Pravuz/AimBot/3D model/Rendered images/Back view.JPG

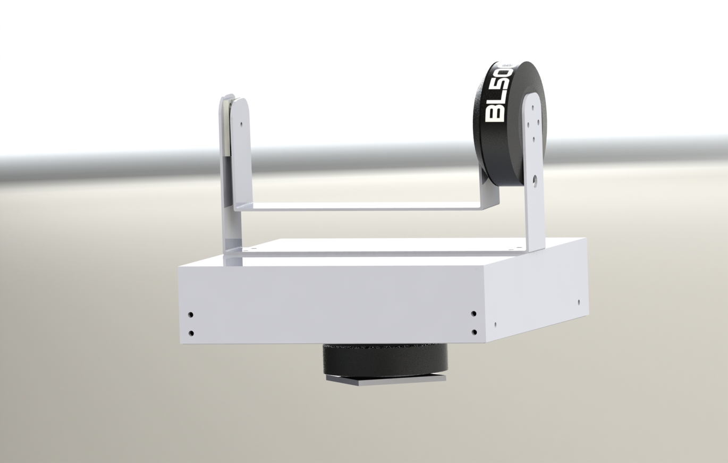
3D model/Rendered images/Back view.JPG
