Pravuz/AimBot/3D model/Rendered images/Bearing and bracket.JPG

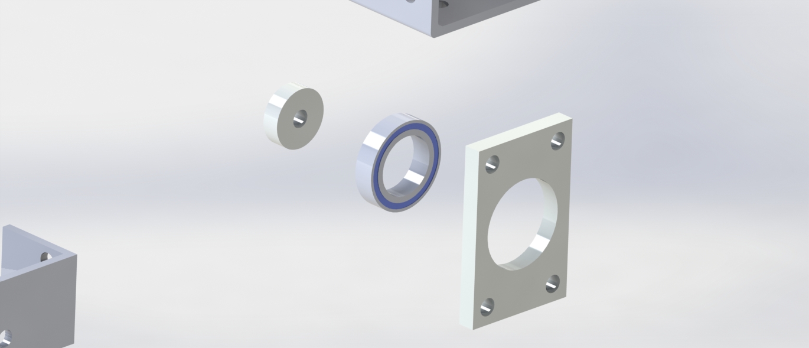
3D model/Rendered images/Bearing and bracket.JPG
