Pravuz/AimBot/3D model/Rendered images/Bottom.JPG

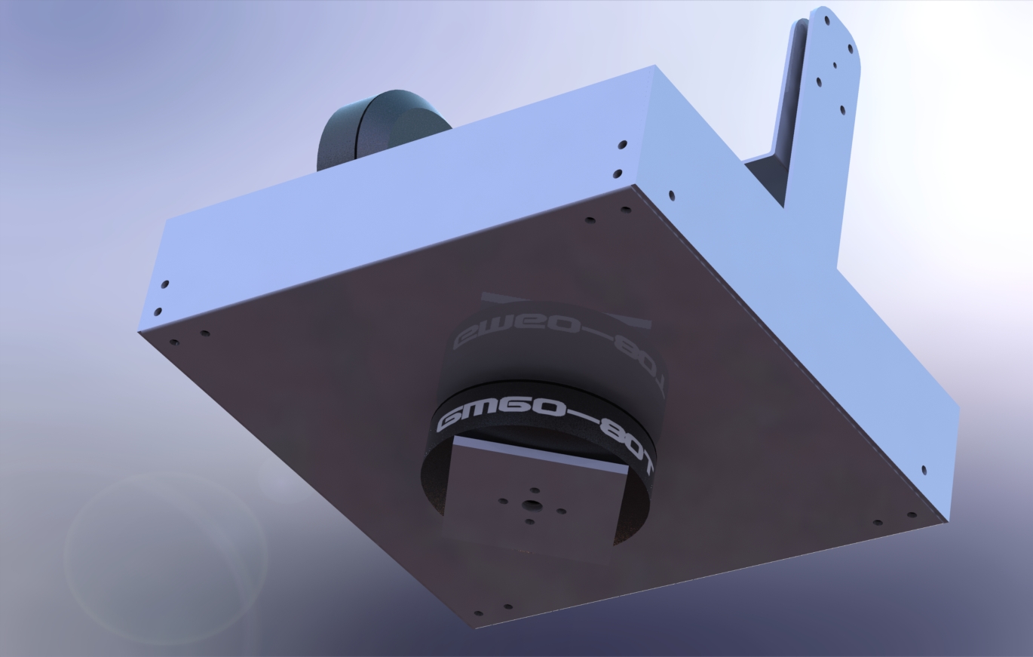
3D model/Rendered images/Bottom.JPG
