Pravuz/AimBot/3D model/Rendered images/Craddle- no hood.JPG

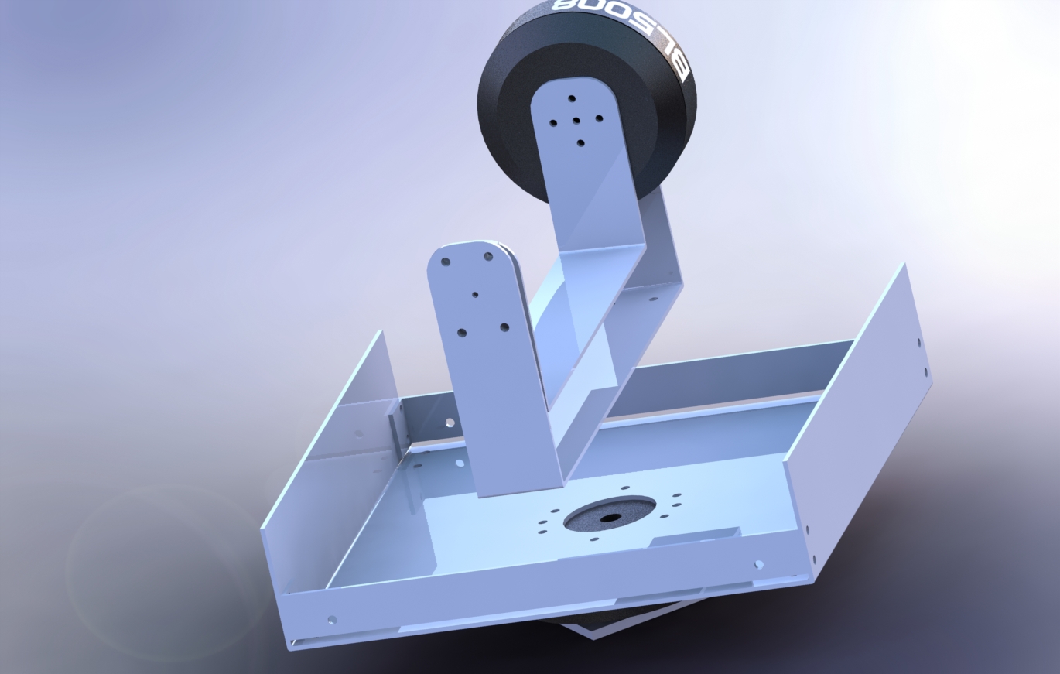
3D model/Rendered images/Craddle- no hood.JPG
