Pravuz/AimBot/3D model/Rendered images/Frontview.JPG

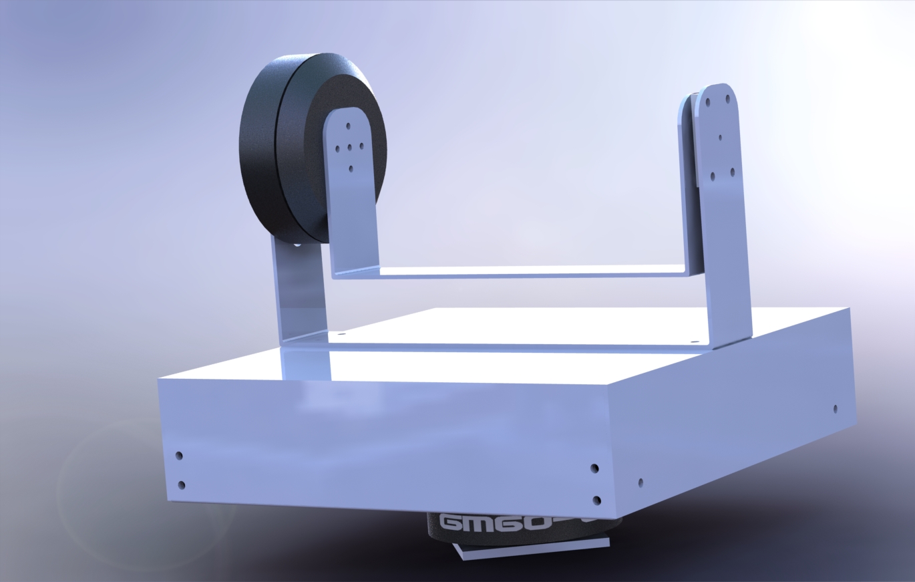
3D model/Rendered images/Frontview.JPG
