Pravuz/AimBot/3D model/Rendered images/No craddle-no hood.JPG

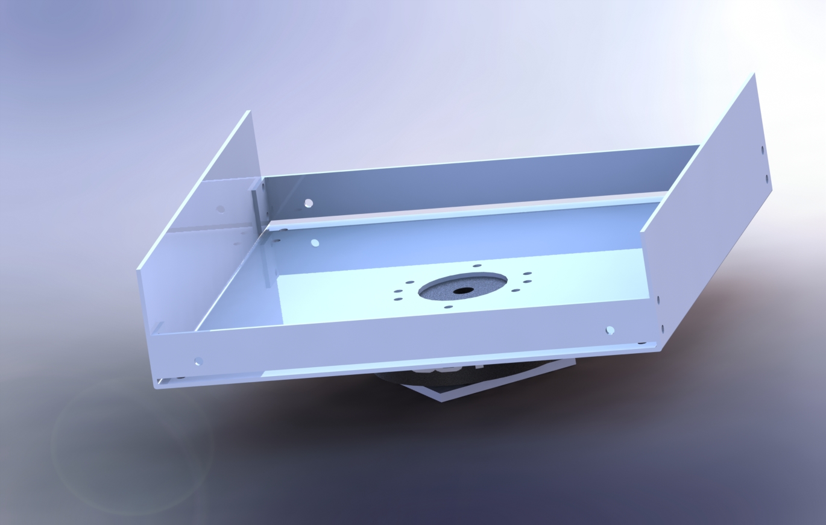
3D model/Rendered images/No craddle-no hood.JPG
