Pravuz/AimBot/3D model/Rendered images/Side - Right.JPG

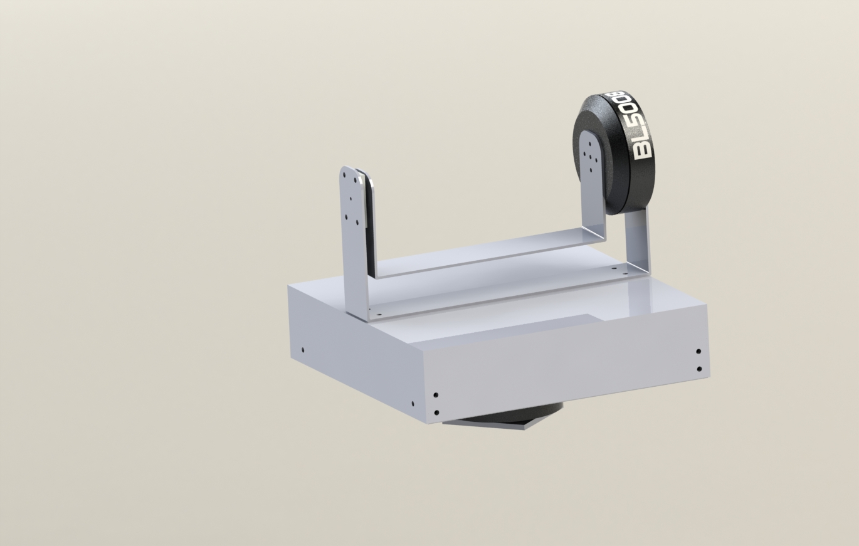
3D model/Rendered images/Side - Right.JPG
