Pravuz/AimBot/3D model/Rendered images/Tripod mount quarter inch.JPG

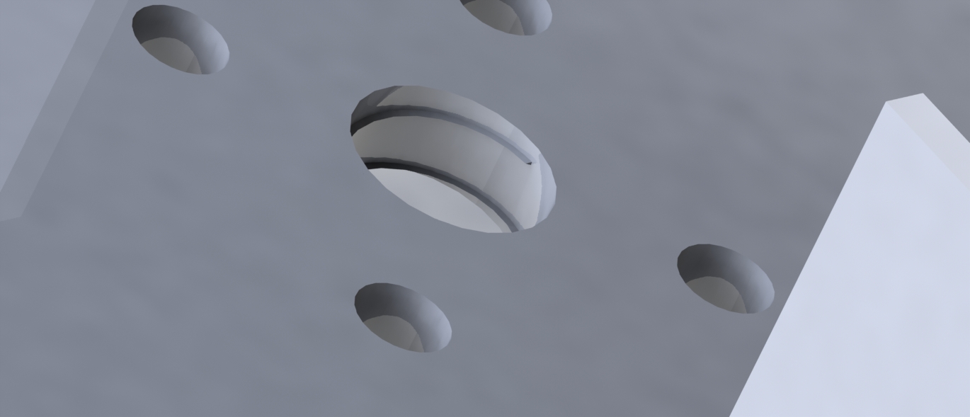
3D model/Rendered images/Tripod mount quarter inch.JPG
