Pravuz/AimBot/Desktop/Aimbot(C++)/Aimbot(C++)/A-Tea.png

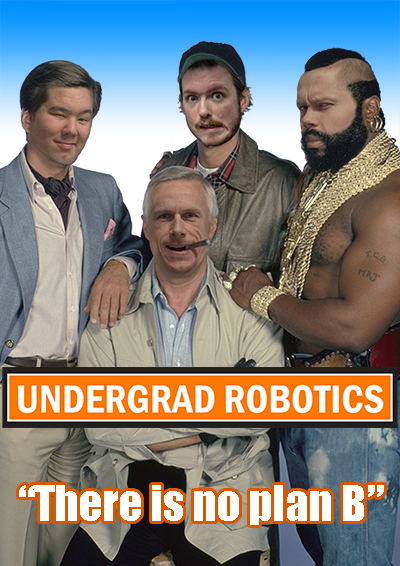
Desktop/Aimbot(C++)/Aimbot(C++)/A-Tea.png
