Pravuz/AimBot/3D model/Assembly 13 - 2 axis/Kulelager/Kulelager.SLDPRT

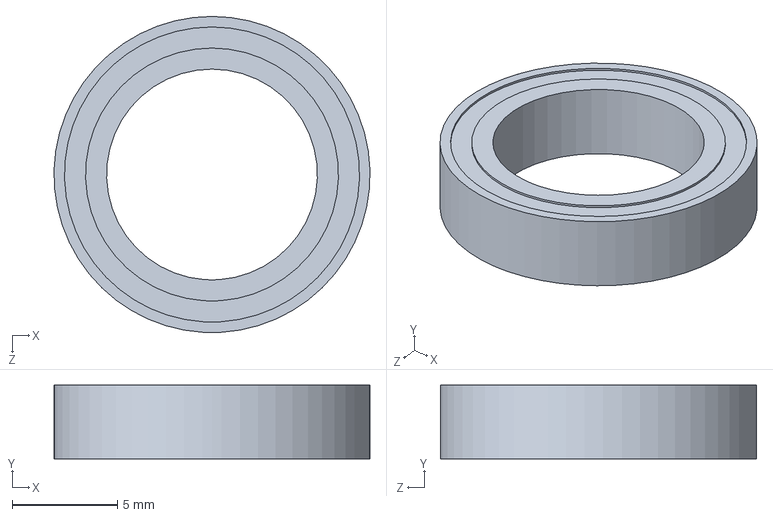
[picture p27: CAD file, 2015-06-03]
3D model/Assembly 13 - 2 axis/Kulelager/Kulelager.SLDPRT
15.0 x 3.50 x 15.0 mm
