Pravuz/AimBot/3D model/Assembly 13 - 2 axis/Parts/side-L.SLDPRT

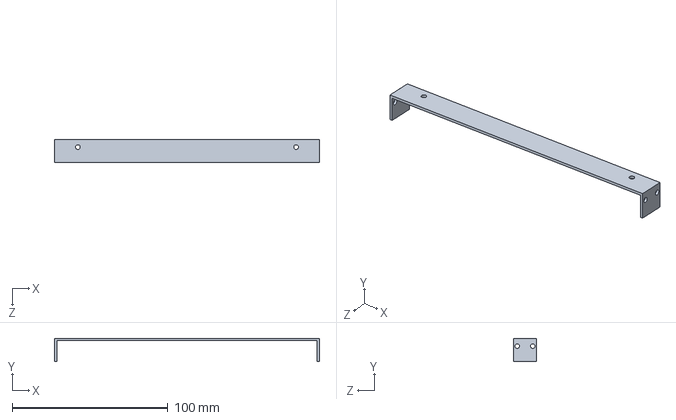
[picture p28: CAD file, 2015-06-03]
3D model/Assembly 13 - 2 axis/Parts/side-L.SLDPRT
170.0 x 15.0 x 15.0 mm
