Pravuz/AimBot/3D model/Assembly 14 - 3 axis/quanum-motor-2208-1.snapshot.4/QUANUM GIMBAL MOTOR 2208 BASE.SLDPRT

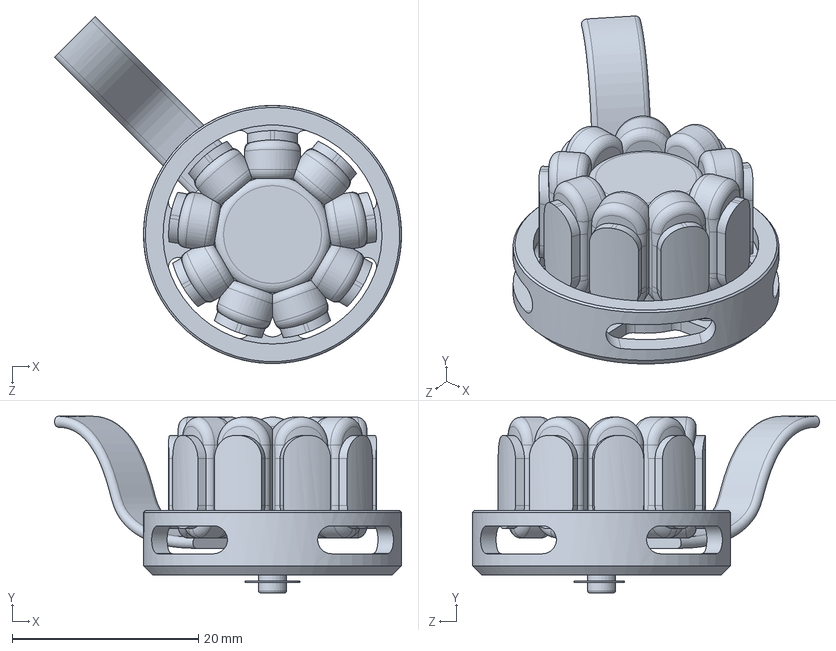
[picture p29: CAD file, 2015-06-03]
3D model/Assembly 14 - 3 axis/quanum-motor-2208-1.snapshot.4/QUANUM GIMBAL MOTOR 2208 BASE.SLDPRT
37.2 x 19.0 x 37.3 mm
