Pravuz/AimBot/3D model/Assembly 13 - 2 axis/Parts/5mm motorholder.SLDPRT

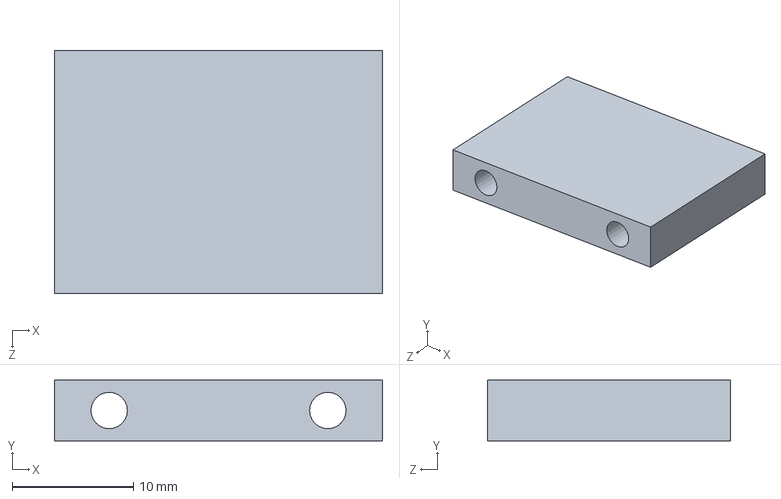
[picture p30: CAD file, 2015-06-03]
3D model/Assembly 13 - 2 axis/Parts/5mm motorholder.SLDPRT
27.0 x 5.00 x 20.0 mm
