Pravuz/AimBot/3D model/Assembly 13 - 2 axis/Parts/L-jern til boks.SLDPRT

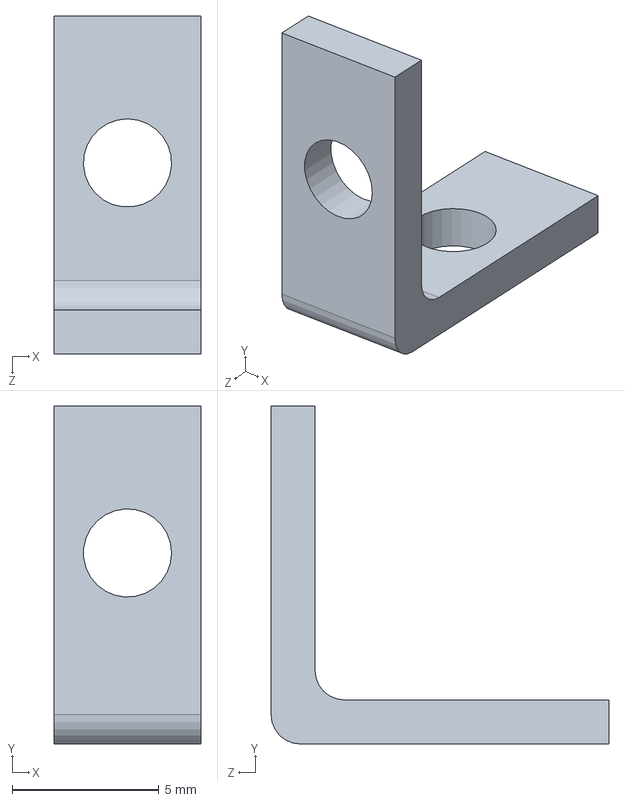
[picture p31: CAD file, 2015-06-03]
3D model/Assembly 13 - 2 axis/Parts/L-jern til boks.SLDPRT
5.00 x 11.5 x 11.5 mm
