Pravuz/AimBot/3D model/Assembly 14 - 3 axis/Parts/øvre L.SLDPRT

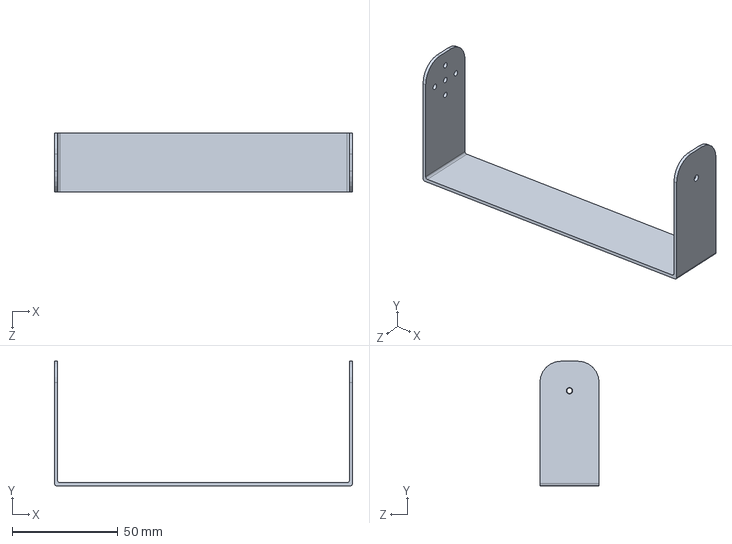
[picture p32: CAD file, 2015-06-03]
3D model/Assembly 14 - 3 axis/Parts/øvre L.SLDPRT
141.0 x 59.0 x 28.0 mm
