Pravuz/AimBot/3D model/Assembly 14 - 3 axis/Parts/unnerplate.SLDPRT

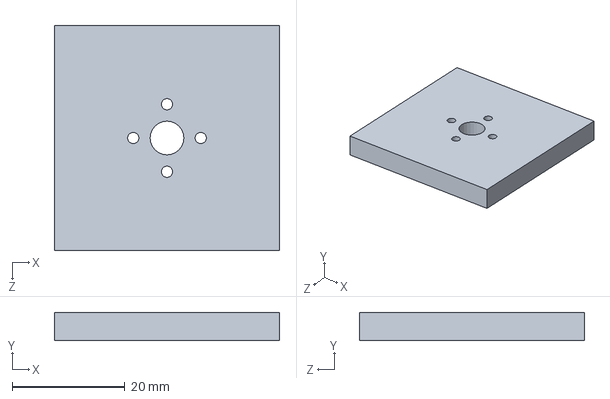
[picture p33: CAD file, 2015-06-03]
3D model/Assembly 14 - 3 axis/Parts/unnerplate.SLDPRT
40.0 x 5.00 x 40.0 mm
