Pravuz/AimBot/3D model/Assembly 13 - 2 axis/Parts/Bunnplate til boks.SLDPRT

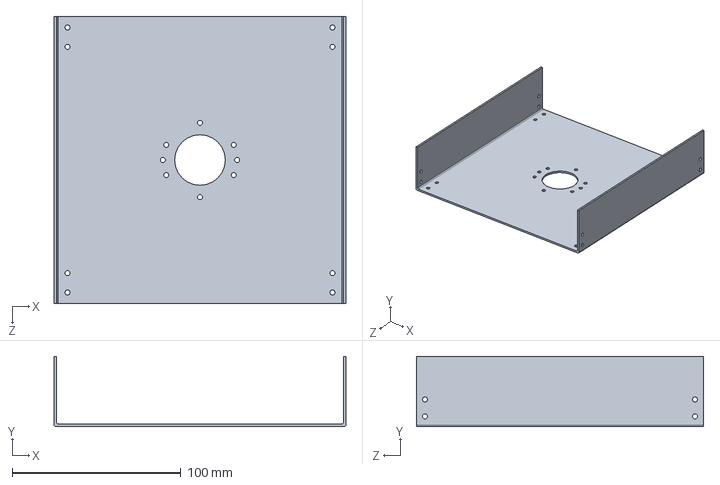
[picture p34: CAD file, 2015-06-03]
3D model/Assembly 13 - 2 axis/Parts/Bunnplate til boks.SLDPRT
173.0 x 41.5 x 170.0 mm
