Pravuz/AimBot/3D model/Assembly 13 - 2 axis/Parts/topp motorbru.SLDPRT

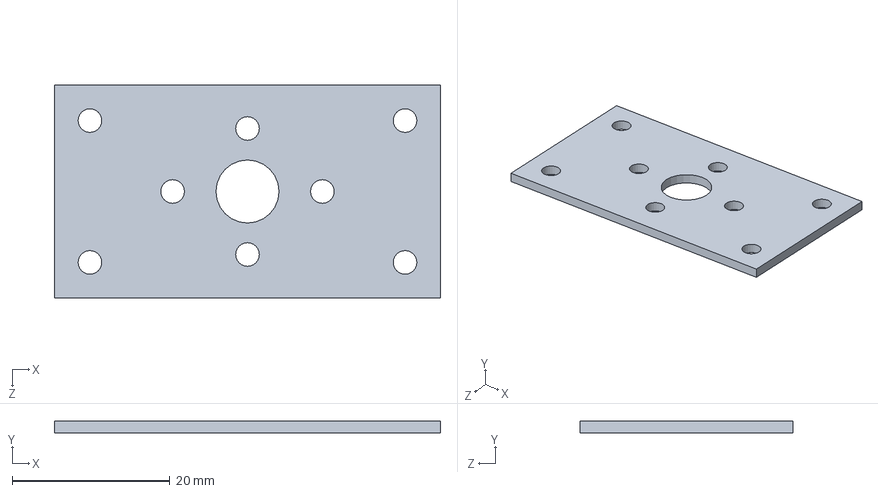
[picture p35: CAD file, 2015-06-03]
3D model/Assembly 13 - 2 axis/Parts/topp motorbru.SLDPRT
49.0 x 1.50 x 27.0 mm
