Pravuz/AimBot/3D model/Assembly 14 - 3 axis/Parts/midtre L 1.SLDPRT

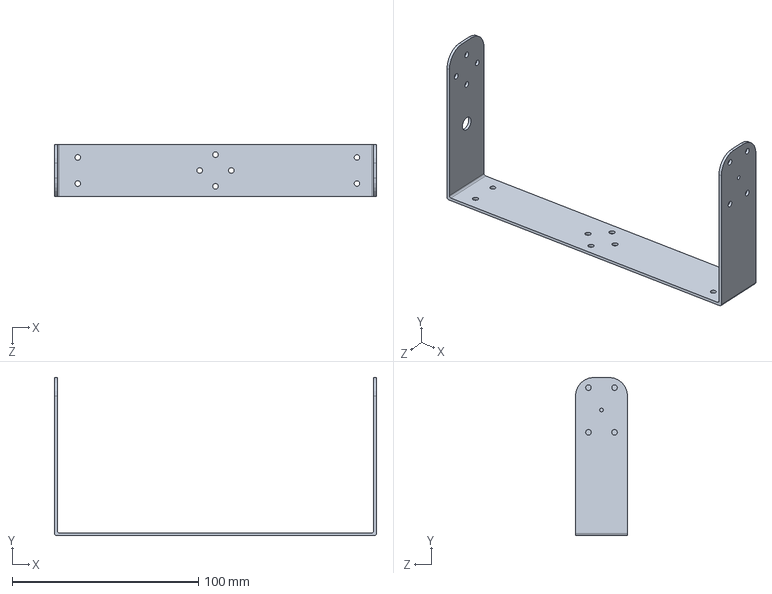
[picture p36: CAD file, 2015-06-03]
3D model/Assembly 14 - 3 axis/Parts/midtre L 1.SLDPRT
173.0 x 85.0 x 28.0 mm
