Pravuz/AimBot/3D model/Assembly 13 - 2 axis/Parts/topplate.SLDPRT

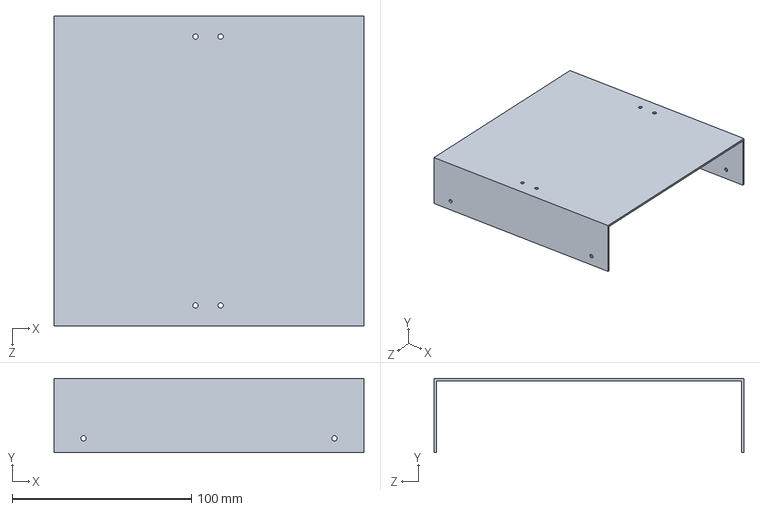
[picture p37: CAD file, 2015-06-03]
3D model/Assembly 13 - 2 axis/Parts/topplate.SLDPRT
173.0 x 41.5 x 173.0 mm
