Pravuz/AimBot/3D model/Assembly 13 - 2 axis/GM60-80T/motormodel decal.png

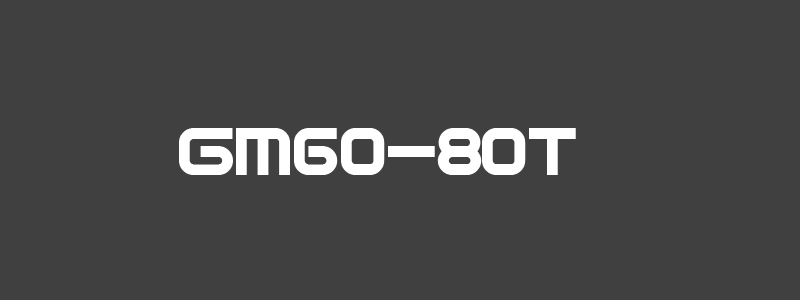
3D model/Assembly 13 - 2 axis/GM60-80T/motormodel decal.png
