Pravuz/AimBot/3D model/Assembly 13 - 2 axis/quanum-motor-2208-1.snapshot.4/QUANUM GIMBAL MOTOR 2208 ASM.JPG

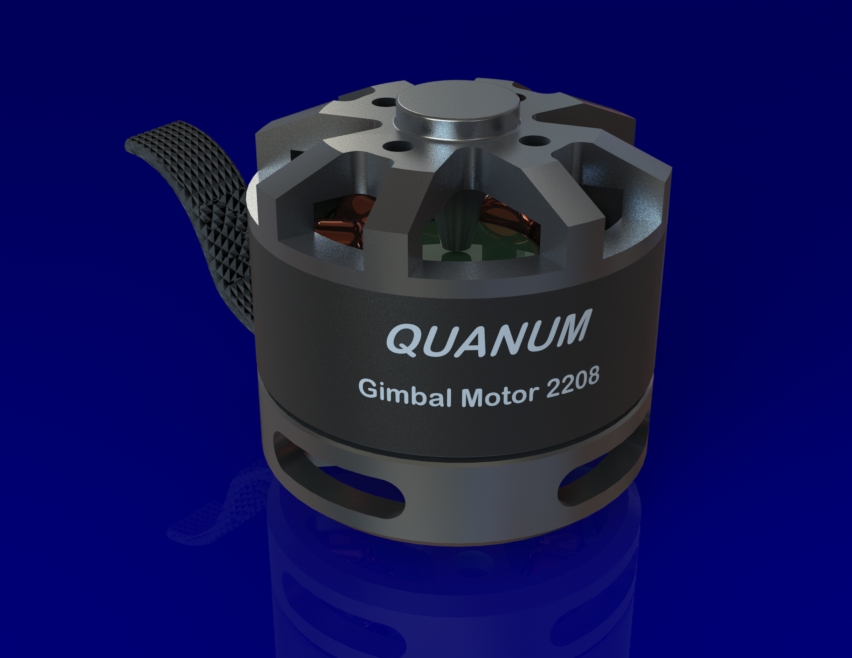
3D model/Assembly 13 - 2 axis/quanum-motor-2208-1.snapshot.4/QUANUM GIMBAL MOTOR 2208 ASM.JPG
