Pravuz/AimBot/Pixy/gcc/video/inc/chip.h

/*
 * @brief Chip inclusion selector file
 *
 * Copyright(C) NXP Semiconductors, 2013
 * All rights reserved.
 *
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
 * Permission to use, copy, modify, and distribute this software and its
 * documentation is hereby granted, under NXP Semiconductors' and its
 * licensor's relevant copyrights in the software, without fee, provided that it
 * is used in conjunction with NXP Semiconductors microcontrollers.  This
 * copyright, permission, and disclaimer notice must appear in all copies of
 * this code.
 */

#ifndef __CHIP_H_
#define __CHIP_H_

//#include "sys_config.h"
//#include "cmsis.h"

#if defined(CHIP_LPC18XX)
#include "chip_lpc18xx.h"

#elif defined(CHIP_LPC43XX)
#include "chip_lpc43xx.h"

#else
#error CHIP_LPC18XX or CHIP_LPC43XX must be defined
#endif

/* Aliasing for Chip_USB_Init */
#define Chip_USB_Init  Chip_USB0_Init

#ifdef __cplusplus
extern "C"
{
#endif

/** @ingroup CHIP_18XX_43XX_DRIVER_OPTIONS
 * @{
 */

/**
 * @brief	System oscillator rate
 * This value is defined externally to the chip layer and contains
 * the value in Hz for the external oscillator for the board. If using the
 * internal oscillator, this rate can be 0.
 */
extern const uint32_t OscRateIn;

/**
 * @brief	Clock rate on the CLKIN pin
 * This value is defined externally to the chip layer and contains
 * the value in Hz for the CLKIN pin for the board. If this pin isn't used,
 * this rate can be 0.
 */
extern const uint32_t ExtRateIn;

/**
 * @}
 */

/** @defgroup SUPPORT_18XX_43XX_FUNC CHIP: LPC18xx/43xx support functions
 * @ingroup CHIP_18XX_43XX_Drivers
 * @{
 */

/**
 * @brief	Current system clock rate, mainly used for sysTick
 */
extern uint32_t SystemCoreClock;

/**
 * @brief	Update system core clock rate, should be called if the
 *			system has a clock rate change
 * @return	None
 */
void SystemCoreClockUpdate(void);

/**
 * @brief USB0 Pin and clock initialization
 * Calling this function will initialize the USB0 pins and the clock
 * @note This function will assume that the chip is clocked by an
 * external crystal oscillator of frequency 12MHz
 */
void Chip_USB0_Init(void);

/**
 * @brief USB1 Pin and clock initialization
 * Calling this function will initialize the USB0 pins and the clock
 * @note This function will assume that the chip is clocked by an
 * external crystal oscillator of frequency 12MHz
 */
void Chip_USB1_Init(void);

/**
 * @brief	Set up and initialize hardware prior to call to main()
 * @return	None
 * @note	Chip_SystemInit() is called prior to the application and sets up
 * system clocking prior to the application starting.
 */
void Chip_SystemInit(void);

/**
 * @brief	Clock and PLL initialization based on the external oscillator
 * @return	None
 * @note	This function assumes an external crystal oscillator
 * frequency of 12MHz.
 */
void Chip_SetupXtalClocking(void);

/**
 * @brief	Clock and PLL initialization based on the internal oscillator
 * @return	None
 */
void Chip_SetupIrcClocking(void);

/**
 * @}
 */

#ifdef __cplusplus
}
#endif

#endif /* __CHIP_H_ */
