Pravuz/AimBot/Arduino/Unit tests/SAFF-MEGA 2 working beta 18 mai/SAFF-MEGA.ino

//#define __DEBUG
#define __MEGA
#include "Aimbot_Serial.h"
#include "eeprom.h"
#include "Aimbot_EEPROM.h"

// Interrupt numbers for each PWM chanel
#define CHAN1_INTERRUPT		3	// pin 20
#define CHAN2_INTERRUPT		4	// pin 19
#define CHAN3_INTERRUPT		5	// pin 18
#define CHAN4_INTERRUPT		2	// pin 21
#define CHAN1_DIGIN			20	
#define CHAN2_DIGIN			19	
#define CHAN3_DIGIN			18	
#define CHAN4_DIGIN			21	

// Power switching
#define ESC_PWR				2
#define PIX_PWR				3
#define FPV_PWR				4

// Camera (GoPro/DSLR)
int CAM_BTN_DELAY = 100;
int CAM_TRIGGER_DELAY = 500;
int CAM_FOCUS_DELAY = 200;
#define CAM_TRIGGER			6
#define CAM_FOCUS			7

// USB
#define USBconnectedPIN		26
#define USBpulldownPIN		28
bool USBisConnected = false;
bool megaDebug = DEBUG;

// RC defs
int xRCmin = 1916;
int xRCmax = 1052;
int xRCMAPmin = -10;
int xRCMAPmax = 10;
int yRCmin = 1040;
int yRCmax = 1916;
int yRCMAPmin = -10;
int yRCMAPmax = 10;
int xVECT_INmin = -127;
int xVECT_INmax = 127;
int xVECT_OUTmin = -30;
int xVECT_OUTmax = 30;
int yVECT_INmin = -98;
int yVECT_INmax = 98;
int yVECT_OUTmin = -16;
int yVECT_OUTmax = 16;

enum Aimbot_Mode
{
	SLEEP_MODE,
	AUTO,
	MANUAL,
}currentMode;

// PWM-in related vars
int lastRCvalCH1 = 0;  // cam trigger (gear)
int lastRCvalCH2 = 0;  // L/R (Left = 1916) (RIGHT = 1052)
int lastRCvalCH3 = 0;  // mode select (flap gyro)
int lastRCvalCH4 = 0;  // up down (UP = 1916, DOWN = 1052)

//timing, volatile due to interrupts
volatile unsigned long oldtime1 = 0;
volatile int timepassed1;
volatile unsigned long oldtime2 = 0;
volatile int timepassed2;
volatile unsigned long oldtime3 = 0;
volatile int timepassed3;
volatile unsigned long oldtime4 = 0;
volatile int timepassed4;

// Take picture routine
int lastPictureTime = 0;
bool isDSLR = false;

// Mode/loop related
volatile unsigned long lastPassTime = 0;
volatile bool isFirstAuto = true;
int LOOP_TIME = 50;
bool modeSequenceHasBeenDone = false; // At each restart mode has to go to sleep before start to avoid
// sudden start in auto/RC with bad consecuences
uint8_t pixyUpdateCount = 0;

// Serial interface
static AimBot_Serial m_pixySerial(Serial3);
static AimBot_Serial m_escSerial(Serial2);
String inString = "";  // buffer for PC communication

void setup()
{
	// Load config from persistent storage
	//loadSettingsFromEEPROM();

	// Setup serial
	if(megaDebug || isUSBconnected()) Serial.begin(BAUDRATE);	// Usb debug
	if(megaDebug) Serial.println("Setup started");
	Serial2.begin(BAUDRATE); //m_pixySerial begin
	Serial3.begin(BAUDRATE); //m_escSerial begin

	// Initial Mode
	currentMode = SLEEP_MODE; // Start with externals off

	// USB setup
	pinMode(USBpulldownPIN, OUTPUT);
	pinMode(USBconnectedPIN, INPUT);
	digitalWrite(USBpulldownPIN, LOW);

	// RC channels
	pinMode(CHAN1_DIGIN, INPUT); // gear 
	pinMode(CHAN2_DIGIN, INPUT); // aile 
	pinMode(CHAN3_DIGIN, INPUT); // elev 
	pinMode(CHAN4_DIGIN, INPUT); // rudd 

	// power pins
	pinMode(CAM_TRIGGER, OUTPUT);
	pinMode(CAM_FOCUS, OUTPUT);
	pinMode(ESC_PWR, OUTPUT);
	pinMode(FPV_PWR, OUTPUT);
	digitalWrite(PIX_PWR, LOW); // Turn off Pixy power
	digitalWrite(ESC_PWR, LOW); // Turn off Brugi power
	digitalWrite(FPV_PWR, LOW); // Turn off Video transmitter power

	//Start mode selector interrupt (on RC channels)
	attachInterrupt(CHAN4_INTERRUPT, calculatePWMch4, CHANGE);
	attachInterrupt(CHAN3_INTERRUPT, calculatePWMch3, CHANGE);
	attachInterrupt(CHAN2_INTERRUPT, calculatePWMch2, CHANGE);
	attachInterrupt(CHAN1_INTERRUPT, calculatePWMch1, CHANGE);

	if (megaDebug) Serial.println("Setup complete");
}

void loop()
{
	if (isUSBconnected() && !megaDebug) // Settings & debug
	{
		communicateWithPC();
	}
	if(modeSequenceHasBeenDone) // normal operation:
	{
		if (checkCameraTrigger())
		{
			if (currentMode == SLEEP_MODE) timelapseMode();
			else takePicture(); // Check trigger and take picture if pressed
		}

		long diff = millis() - lastPassTime;
		if (diff > LOOP_TIME)
		{
			// Run update for the current mode
			switch (currentMode)
			{
			case AUTO:
				Mode_Auto();
				break;
			case MANUAL:
				Mode_Manual();
				break;
			default:
				break;
			}
			lastPassTime = millis();
		}
	}
}
void Mode_Auto()
{
	if (isFirstAuto)
	{
		isFirstAuto = false;
		// Wait for Brugi feedback (brugi in position after init)
		while (Serial2.available() < 1){ delay(1); }
		while (Serial2.available() > 0){ Serial2.read(); }
		m_pixySerial.pixyCmd(PIXY_START); // Start pixy
		pixyUpdateCount = 0;
		return; //pixy wont respond immediatly, so we don't need to continue here. 
	}
	if (!m_pixySerial.update()){
		pixyUpdateCount++;
		// Making sure pixy is running, if it is then nothing happens. if it's not, then this will make sure it is. 
		if (pixyUpdateCount >= 20){ 
			m_pixySerial.pixyCmd(PIXY_START); 
			pixyUpdateCount = 0;
		}
		return; // update failed, nothing more to do, returning
	} 


	char x = getVECTx(m_pixySerial.getX());
	char y = getVECTy(m_pixySerial.getY());

	//todo: add distance filter, not moving if movement is small. but take picture.
	if (x | y)
	{
		m_escSerial.sendXY(x, y, VECTOR); // Send to Brugi if any movement
		uint8_t timeout = 200;
		// Wait for Brugi feedback (brugi in position)
		while (Serial2.available() == 0)
		{ 
			if (timeout==0) break; //esc did not reach position, but continue regardless. 
			if(megaDebug) Serial.println("waiting"); 
			delay(10); 
			timeout--;
		}
		while (Serial2.available() > 0){ Serial2.read(); }
		//waiting for rig to settle
		delay(250);

		takePicture(); // Arrived at destination, take picture

		//flush both serials, reset
		m_pixySerial.flush();
		m_escSerial.flush();

		m_pixySerial.pixyCmd(PIXY_START); // Start pixy again
	}
}

void Mode_Manual()
{
	char x = getRCx();
	char y = getRCy();

	// Send to Brugi if any movement (or 0)
	m_escSerial.sendXY(x, y, MOV_XY);
}

// Helper routines--------------------------------------------------------------------------
bool checkCameraTrigger()
{
	// check if trigger is pressed
	if (lastRCvalCH1 > 1500) return true;
	else return false;
}

void takePicture()
{

	if (isDSLR) // DSLR's require focus before trigger
	{
		// Check that there is a set time between pictures
		int diff = millis() - lastPictureTime;
		if (diff > CAM_TRIGGER_DELAY)
		{
			digitalWrite(CAM_FOCUS, HIGH);
			delay(CAM_FOCUS_DELAY);
			digitalWrite(CAM_FOCUS, LOW);
			digitalWrite(CAM_TRIGGER, HIGH);
			delay(CAM_BTN_DELAY);
			digitalWrite(CAM_TRIGGER, LOW);
			lastPictureTime = millis();
		}
	}
	else
	{
		int diff = millis() - lastPictureTime;
		if (diff > CAM_TRIGGER_DELAY)
		{
			if(megaDebug) Serial.println("PICTURE!");
			digitalWrite(CAM_TRIGGER, HIGH);
			delay(CAM_BTN_DELAY);
			digitalWrite(CAM_TRIGGER, LOW);
			lastPictureTime = millis();
		}
	}
}
void timelapseMode() // takes a timelapse burst of 100 photos
{
	digitalWrite(ESC_PWR, HIGH); // Turn on Brugi power
	delay(2000); // wait a bit 
	for (int i = 0; i < 100; i++)
	{
		delay(2000); // wait
		digitalWrite(CAM_TRIGGER, HIGH); // take picture
		delay(CAM_BTN_DELAY);
		digitalWrite(CAM_TRIGGER, LOW);
		delay(2000);
		m_escSerial.sendXY(10, 10, VECTOR); // move rig
		if (currentMode != SLEEP_MODE) // stop timelapse if mode is switched
		{
			while (Serial2.available() > 0){ Serial2.read(); } // flush buffer
			break;
		}
	}
	digitalWrite(ESC_PWR, LOW); // Turn off Brugi power again

}


char getRCx()
{
	// Map RC vals to degrees, X
	return (char)map(lastRCvalCH2, xRCmin, xRCmax, xRCMAPmin, xRCMAPmax);
}
char getRCy()
{
	// Map RC vals to degrees, Y
	return (char)map(lastRCvalCH4, yRCmin, yRCmax, yRCMAPmin, yRCMAPmax);
}

char getVECTx(char x)
{
	// Map pixy pixel-vector to degrees, X
	if (x == 0) return 0;
	return (char)map(x, xVECT_INmin, xVECT_INmax, xVECT_OUTmin, xVECT_OUTmax);
}
char getVECTy(char y)
{
	// Map pixy pixel-vector to degrees, Y
	if (y == 0) return 0;
	return (char)map(y, yVECT_INmin, yVECT_INmax, yVECT_OUTmin, yVECT_OUTmax);
}

void calculatePWMch1() // Gear
{
	timepassed1 = micros() - oldtime1;
	oldtime1 = micros();

	if (timepassed1 > 900 && timepassed1 < 2100) lastRCvalCH1 = timepassed1;
}
void calculatePWMch2() // Aile
{
	timepassed2 = micros() - oldtime2;
	oldtime2 = micros();

	if (timepassed2 > 900 && timepassed2 < 2100) lastRCvalCH2 = timepassed2;
}
void calculatePWMch3() // Mode selector
{
	// Mode select uses ORX flap gyro switch with 3 modes
	timepassed3 = micros() - oldtime3;
	oldtime3 = micros();

	if (timepassed3 < 2100 && timepassed3 > 900)
	{
		lastRCvalCH3 = timepassed3;
		if (timepassed3 > 1800){
			if (currentMode != MANUAL && modeSequenceHasBeenDone){
				// Manual, no pixy feed
				digitalWrite(PIX_PWR, LOW);
				digitalWrite(ESC_PWR, HIGH);
				digitalWrite(FPV_PWR, HIGH);
				if (currentMode != MANUAL && megaDebug) Serial.println("Mode is now set to MANUAL");
			}
			currentMode = MANUAL;
		}
		else if (timepassed3 > 1200)  {
			if (currentMode != SLEEP_MODE)
			{
				digitalWrite(PIX_PWR, LOW); // Turn off Pixy power
				digitalWrite(ESC_PWR, LOW); // Turn off Brugi power
				digitalWrite(FPV_PWR, LOW); // Turn off Video transmitter power
				if (currentMode != SLEEP_MODE && megaDebug) Serial.println("Mode is now set to SLEEP_MODE");
			}
			currentMode = SLEEP_MODE;
			modeSequenceHasBeenDone = true;  // Rig should always be set to sleep mode before normal operation as a 
			// safety precaution
		}
		else {
			if (currentMode != AUTO && modeSequenceHasBeenDone)
			{
				// Auto, no video feed
				digitalWrite(PIX_PWR, HIGH);
				digitalWrite(ESC_PWR, HIGH);
				digitalWrite(FPV_PWR, LOW);
				isFirstAuto = true;
				if (currentMode != AUTO && megaDebug) Serial.println("Mode is now set to AUTO");
			}
			currentMode = AUTO;			
		}
	}
}
void calculatePWMch4() // Elev
{
	timepassed4 = micros() - oldtime4;
	oldtime4 = micros();

	if (timepassed4 > 900 && timepassed4 < 2100) lastRCvalCH4 = timepassed4;
}

bool isUSBconnected()
{
	return digitalRead(USBconnectedPIN);
}

void communicateWithPC()
{
	if (Serial.available() > 0)
	{
		inString += (char)Serial.read(); // Read to bufferstring

		if (inString.length() >= 5) // All commands are 5 chars long
		{
			if (inString == "setup") // Recieve new settings
			{
				inString = "";
				int i = 0;
				int settings[21];
				while (i <= 20)
				{
					while (Serial.available() < 1){} // wait for next var
					char last = Serial.read();
					if (last == ',') // comma signals next variable
					{
						settings[i] = inString.toInt();
						inString = "";
						i++;
					}
					else inString += last;
				}

				isDSLR = settings[0]; // no casting, a bool is really a uint8 in disguise
				CAM_BTN_DELAY = settings[1];
				CAM_TRIGGER_DELAY = settings[2];
				CAM_FOCUS_DELAY = settings[3];
				LOOP_TIME = settings[4];
				xRCmin = settings[5];
				xRCmax = settings[6];
				xRCMAPmin = settings[7];
				xRCMAPmax = settings[8];
				yRCmin = settings[9];
				yRCmax = settings[10];
				yRCMAPmin = settings[11];
				yRCMAPmax = settings[12];
				xVECT_INmin = settings[13];
				xVECT_INmax = settings[14];
				xVECT_OUTmin = settings[15];
				xVECT_OUTmax = settings[16];
				yVECT_INmin = settings[17];
				yVECT_INmax = settings[18];
				yVECT_OUTmin = settings[19];
				yVECT_OUTmax = settings[20];
				inString = "";

			}
			else if (inString == "sendx") // Send current settings back
			{
				inString = "";
				Serial.print(isDSLR, DEC); Serial.print(",");
				Serial.print(CAM_BTN_DELAY, DEC); Serial.print(",");
				Serial.print(CAM_TRIGGER_DELAY, DEC); Serial.print(",");
				Serial.print(CAM_FOCUS_DELAY, DEC); Serial.print(",");
				Serial.print(LOOP_TIME, DEC); Serial.print(",");
				Serial.print(xRCmin, DEC); Serial.print(",");
				Serial.print(xRCmax, DEC); Serial.print(",");
				Serial.print(xRCMAPmin, DEC); Serial.print(",");
				Serial.print(xRCMAPmax, DEC); Serial.print(",");
				Serial.print(yRCmin, DEC); Serial.print(",");
				Serial.print(yRCmax, DEC); Serial.print(",");
				Serial.print(yRCMAPmin, DEC); Serial.print(",");
				Serial.print(yRCMAPmax, DEC); Serial.print(",");
				Serial.print(xVECT_INmin, DEC); Serial.print(",");
				Serial.print(xVECT_INmax, DEC); Serial.print(",");
				Serial.print(xVECT_OUTmin, DEC); Serial.print(",");
				Serial.print(xVECT_OUTmax, DEC); Serial.print(",");
				Serial.print(yVECT_INmin, DEC); Serial.print(",");
				Serial.print(yVECT_INmax, DEC); Serial.print(",");
				Serial.print(yVECT_OUTmin, DEC); Serial.print(",");
				Serial.print(yVECT_OUTmax, DEC); Serial.print(",");
				Serial.println(""); // prints newline so it's more convenient when using debug console
			}
			else if (inString == "savex") // Save to EEPROM
			{
				inString = "";
				saveSettingsToEEPROM();
			}
			else
			{
				inString = "";  // Serial might be out of sync, flush bufferstring
			}
			while (Serial.available() > 0)
			{
				Serial.read(); // Flush serial in
			}
		}
	}

}

void saveSettingsToEEPROM()
{
	// Each address on the EEPROM is 8 bits
	int i = 0;
	EEPROMWriteBool(i, isDSLR); i++; // bool uses only one 8bit block
	EEPROMWriteInt16(i, CAM_BTN_DELAY); i++; i++; // an int is 16 bits and uses two blocks
	EEPROMWriteInt16(i, CAM_TRIGGER_DELAY); i++; i++;
	EEPROMWriteInt16(i, CAM_FOCUS_DELAY); i++; i++;
	EEPROMWriteInt16(i, LOOP_TIME); i++; i++;
	EEPROMWriteInt16(i, xRCmin); i++; i++;
	EEPROMWriteInt16(i, xRCmax); i++; i++;
	EEPROMWriteInt16(i, xRCMAPmin); i++; i++;
	EEPROMWriteInt16(i, xRCMAPmax); i++; i++;
	EEPROMWriteInt16(i, yRCmin); i++; i++;
	EEPROMWriteInt16(i, yRCmax); i++; i++;
	EEPROMWriteInt16(i, yRCMAPmin); i++; i++;
	EEPROMWriteInt16(i, yRCMAPmax); i++; i++;
	EEPROMWriteInt16(i, xVECT_INmin); i++; i++;
	EEPROMWriteInt16(i, xVECT_INmax); i++; i++;
	EEPROMWriteInt16(i, xVECT_OUTmin); i++; i++;
	EEPROMWriteInt16(i, xVECT_OUTmax); i++; i++;
	EEPROMWriteInt16(i, yVECT_INmin); i++; i++;
	EEPROMWriteInt16(i, yVECT_INmax); i++; i++;
	EEPROMWriteInt16(i, yVECT_OUTmin); i++; i++;
	EEPROMWriteInt16(i, yVECT_OUTmax); i++; i++;
}

void loadSettingsFromEEPROM()
{
	int i = 0;
	isDSLR = EEPROMReadBool(i); i++;
	CAM_BTN_DELAY = EEPROMReadInt16(i); i++; i++;
	CAM_TRIGGER_DELAY = EEPROMReadInt16(i); i++; i++;
	CAM_FOCUS_DELAY = EEPROMReadInt16(i); i++; i++;
	LOOP_TIME = EEPROMReadInt16(i); i++; i++;
	xRCmin = EEPROMReadInt16(i); i++; i++;
	xRCmax = EEPROMReadInt16(i); i++; i++;
	xRCMAPmin = EEPROMReadInt16(i); i++; i++;
	xRCMAPmax = EEPROMReadInt16(i); i++; i++;
	yRCmin = EEPROMReadInt16(i); i++; i++;
	yRCmax = EEPROMReadInt16(i); i++; i++;
	yRCMAPmin = EEPROMReadInt16(i); i++; i++;
	yRCMAPmax = EEPROMReadInt16(i); i++; i++;
	xVECT_INmin = EEPROMReadInt16(i); i++; i++;
	xVECT_INmax = EEPROMReadInt16(i); i++; i++;
	xVECT_OUTmin = EEPROMReadInt16(i); i++; i++;
	xVECT_OUTmax = EEPROMReadInt16(i); i++; i++;
	yVECT_INmin = EEPROMReadInt16(i); i++; i++;
	yVECT_INmax = EEPROMReadInt16(i); i++; i++;
	yVECT_OUTmin = EEPROMReadInt16(i); i++; i++;
	yVECT_OUTmax = EEPROMReadInt16(i); i++; i++;
}
